benanderman/spork-8/Images/input-3d.png

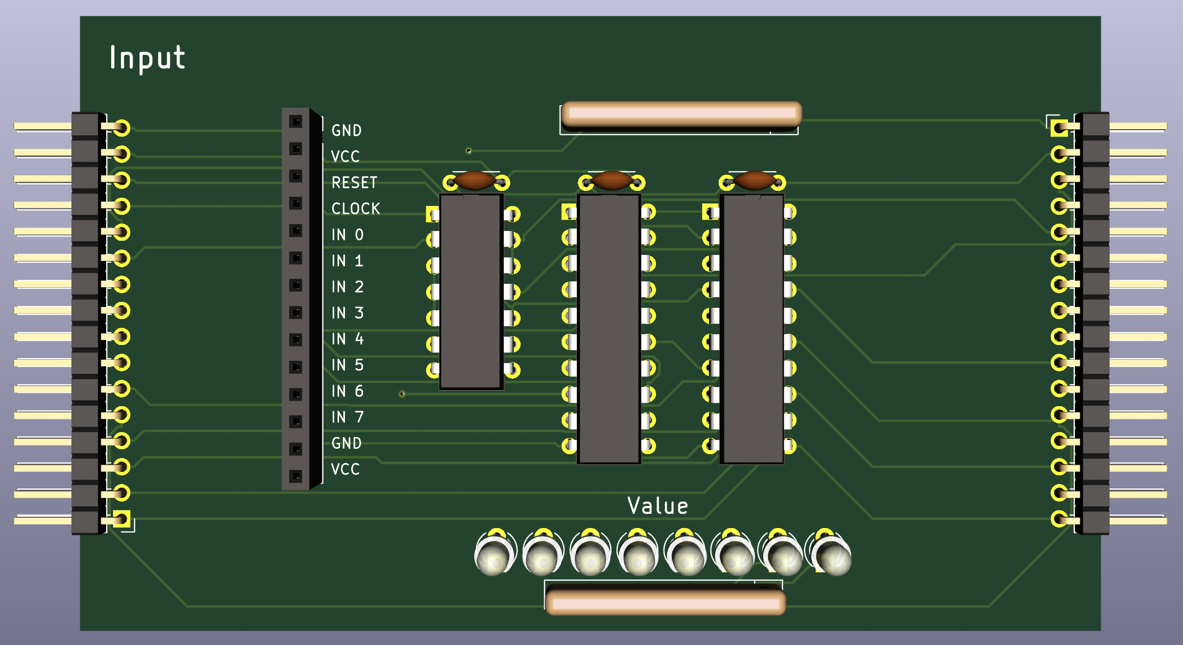
Images/input-3d.png
