benanderman/spork-8/Images/input-pcb.png

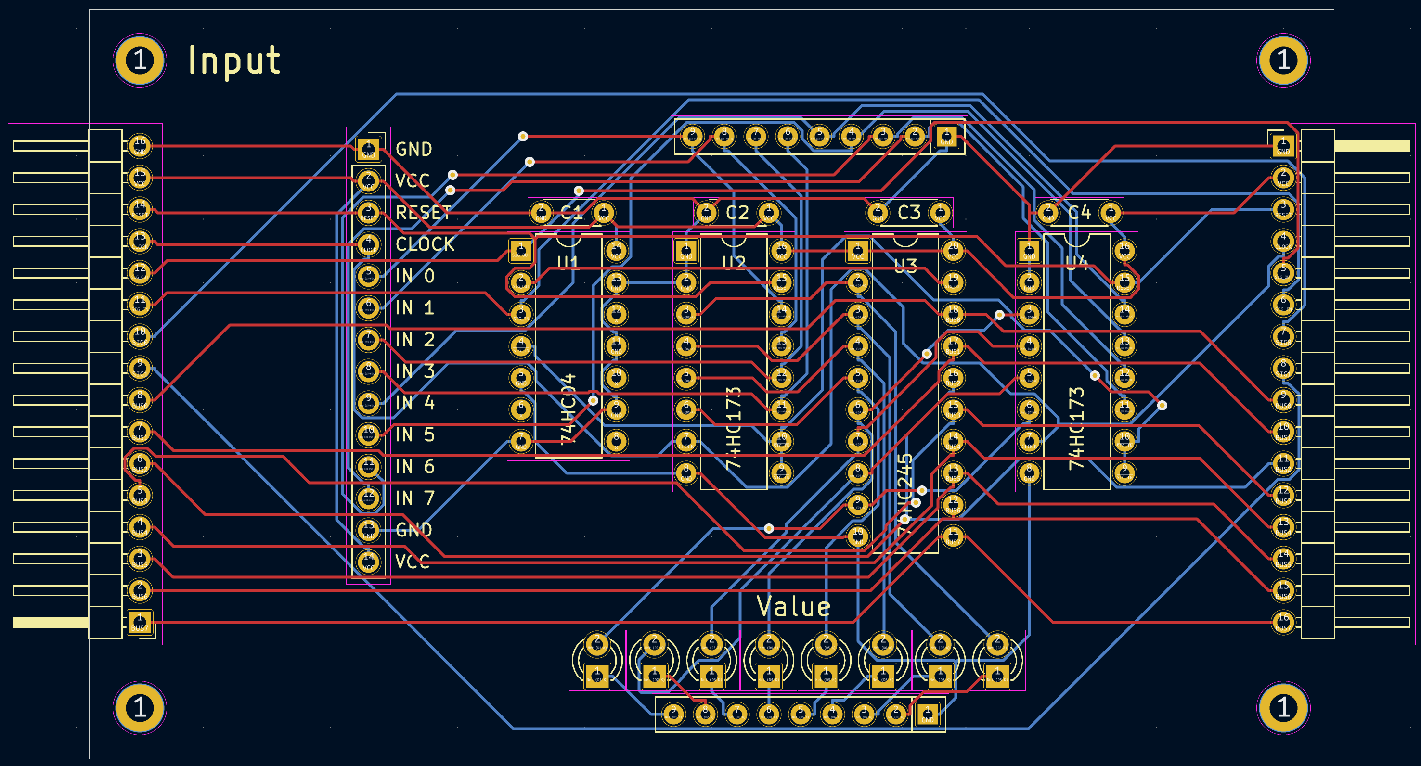
Images/input-pcb.png
