benanderman/spork-8/Images/input-sch.png

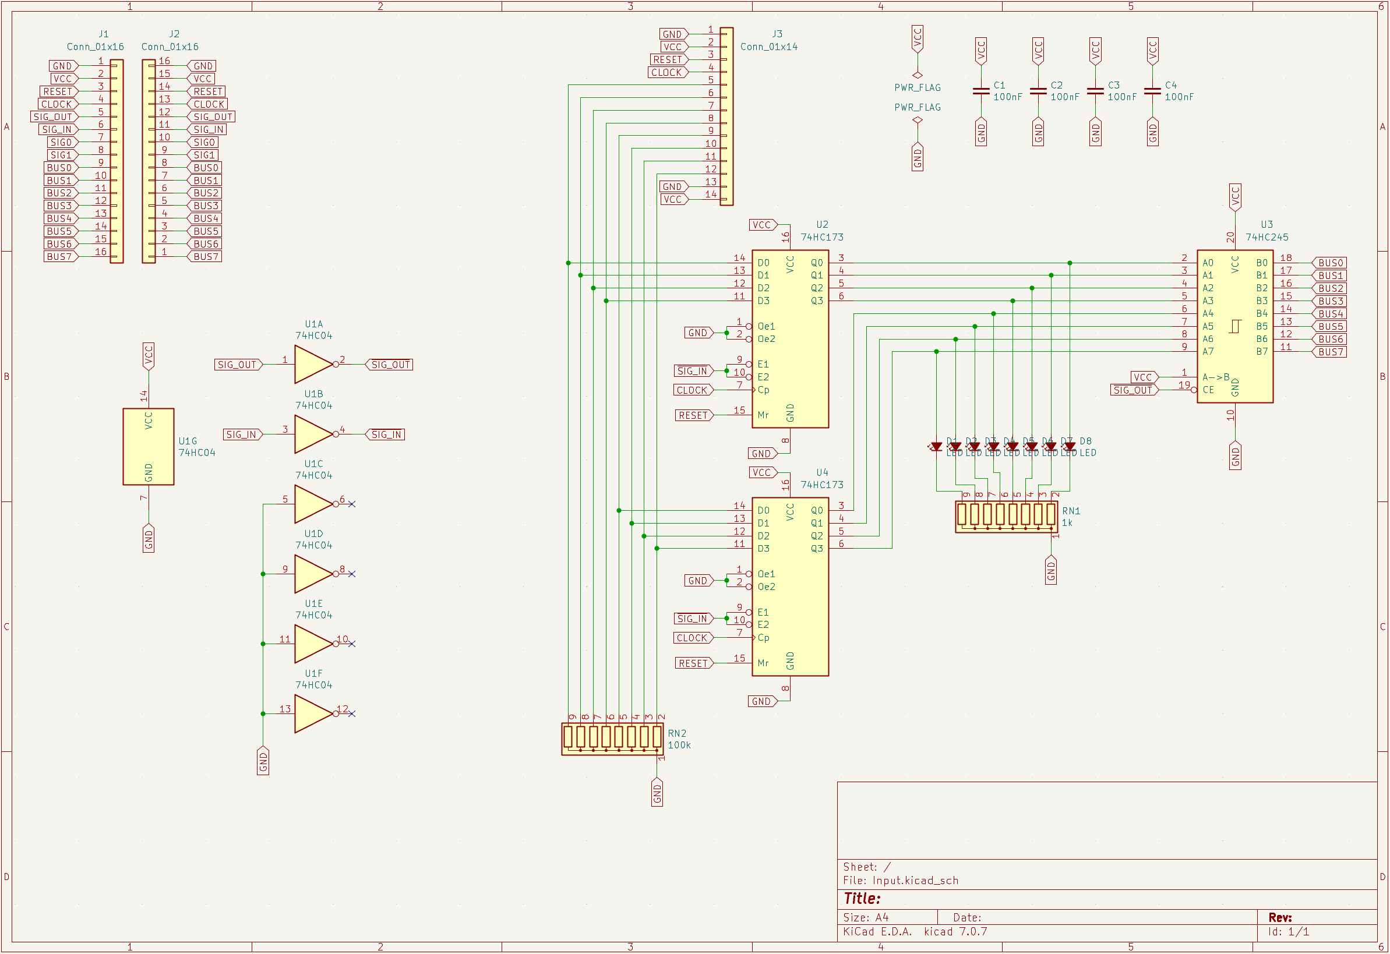
Images/input-sch.png
