benanderman/spork-8/ALU/ALU.kicad_pcb

## KiCad design ALU/ALU.kicad_pcb (2025-06-30)

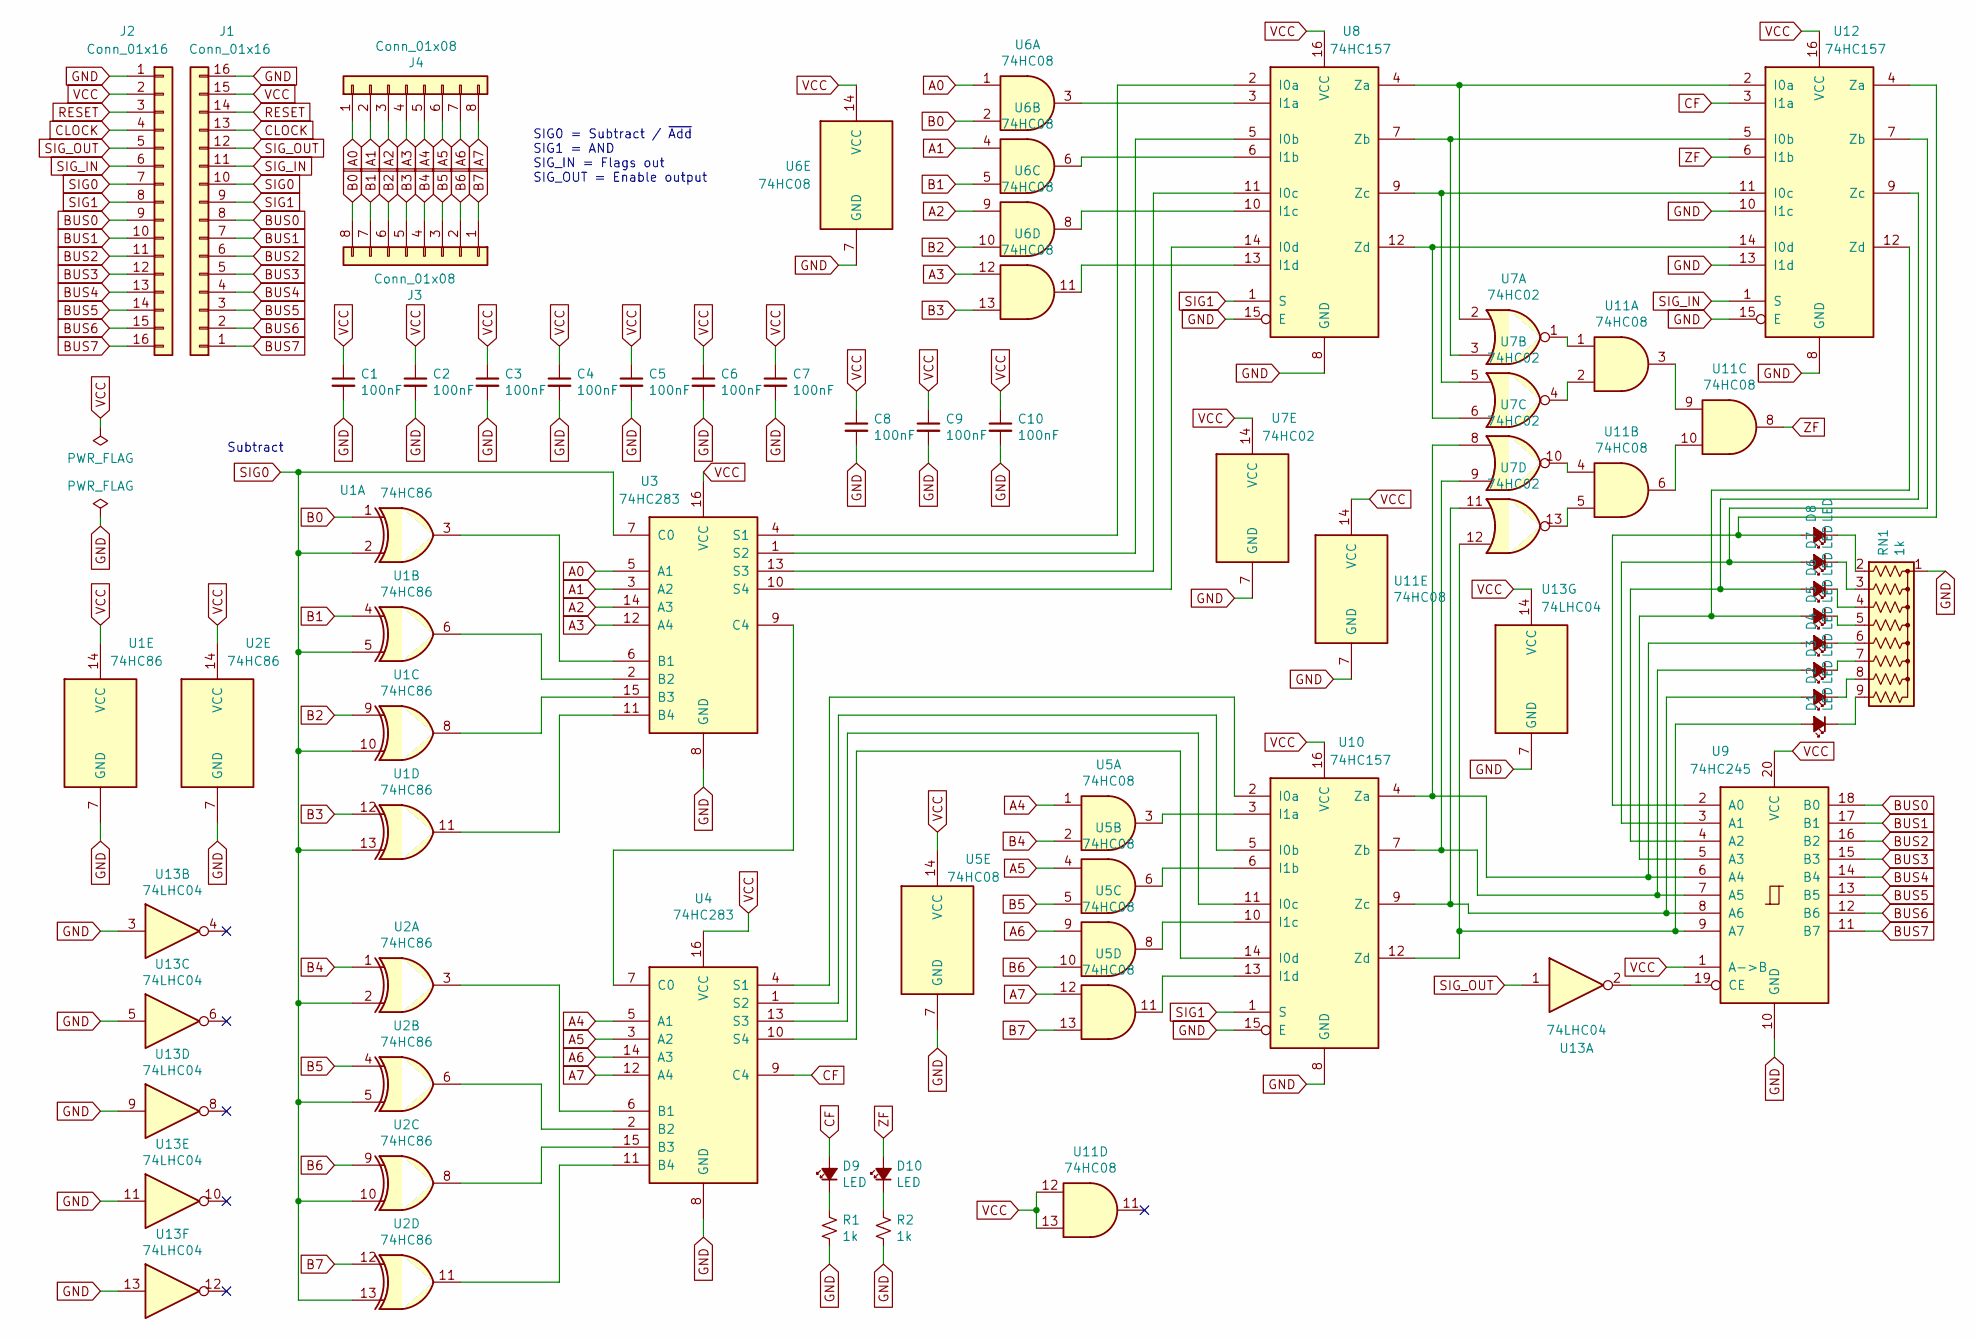
[picture p75: schematic ALU.kicad_sch]

Parts:
C1, C2, C3, C4, C5, C6, C7, C8, C9, C10: 100nF; C_Disc_D4.3mm_W1.9mm_P5.00mm
D1, D2, D3, D4, D5, D6, D7, D8, D9, D10: LED; LED_D3.0mm_Clear
J1, J2: Conn_01x16; PinHeader_1x16_P2.54mm_Horizontal
J3, J4: Conn_01x08; PinHeader_1x08_P2.54mm_Horizontal
R1, R2: 1k; R_Axial_DIN0207_L6.3mm_D2.5mm_P7.62mm_Horizontal
RN1: 1k; R_Array_SIP9
U1, U2: 74HC86; DIP-14_W7.62mm
U3, U4: 74HC283; DIP-16_W7.62mm
U5, U6, U11: 74HC08; DIP-14_W7.62mm
U7: 74HC02; DIP-14_W7.62mm
U8, U10, U12: 74HC157; DIP-16_W7.62mm
U9: 74HC245; DIP-20_W7.62mm
U13: 74LHC04; DIP-14_W7.62mm

Connections:
A0: J4.1, U3.5 (A1), U6.1
A1: J4.2, U3.3 (A2), U6.4
A2: J4.3, U3.14 (A3), U6.9
A3: J4.4, U3.12 (A4), U6.12
A4: J4.5, U4.5 (A1), U5.1
A5: J4.6, U4.3 (A2), U5.4
A6: J4.7, U4.14 (A3), U5.9
A7: J4.8, U4.12 (A4), U5.12
B0: J3.8, U1.1, U6.2
B1: J3.7, U1.4, U6.5
B2: J3.6, U1.9, U6.10
B3: J3.5, U1.12, U6.13
B4: J3.4, U2.1, U5.2
B5: J3.3, U2.4, U5.5
B6: J3.2, U2.9, U5.10
B7: J3.1, U2.12, U5.13
BUS0: J1.8, J2.9, U9.18 (B0)
BUS1: J1.7, J2.10, U9.17 (B1)
BUS2: J1.6, J2.11, U9.16 (B2)
BUS3: J1.5, J2.12, U9.15 (B3)
BUS4: J1.4, J2.13, U9.14 (B4)
BUS5: J1.3, J2.14, U9.13 (B5)
BUS6: J1.2, J2.15, U9.12 (B6)
BUS7: J1.1, J2.16, U9.11 (B7)
CF: D9.2 (A), U4.9 (C4), U12.3 (I1a)
CLOCK: J1.13, J2.4
GND: C1.2, C2.2, C3.2, C4.2, C5.2, C6.2, C7.2, C8.2, C9.2, C10.2, J1.16, J2.1, R1.2, R2.2, RN1.1 (common), U1.7 (GND), U2.7 (GND), U3.8 (GND), U4.8 (GND), U5.7 (GND), U6.7 (GND), U7.7 (GND), U8.8 (GND), U8.15 (E), U9.10 (GND), U10.8 (GND), U10.15 (E), U11.7 (GND), U12.8 (GND), U12.10 (I1c), U12.13 (I1d), U12.15 (E), U13.3, U13.5, U13.7 (GND), U13.9, U13.11, U13.13
unnamed: D1.2 (A), U7.12, U9.9 (A7), U10.12 (Zd)
unnamed: D1.1 (K), RN1.9 (R8)
unnamed: D2.2 (A), U7.11, U9.8 (A6), U10.9 (Zc)
unnamed: D2.1 (K), RN1.8 (R7)
unnamed: D3.2 (A), U7.9, U9.7 (A5), U10.7 (Zb)
unnamed: D3.1 (K), RN1.7 (R6)
unnamed: D4.2 (A), U7.8, U9.6 (A4), U10.4 (Za)
unnamed: D4.1 (K), RN1.6 (R5)
unnamed: D5.2 (A), U9.5 (A3), U12.12 (Zd)
unnamed: D5.1 (K), RN1.5 (R4)
unnamed: D6.2 (A), U9.4 (A2), U12.9 (Zc)
unnamed: D6.1 (K), RN1.4 (R3)
unnamed: D7.2 (A), U9.3 (A1), U12.7 (Zb)
unnamed: D7.1 (K), RN1.3 (R2)
unnamed: D8.2 (A), U9.2 (A0), U12.4 (Za)
unnamed: D8.1 (K), RN1.2 (R1)
unnamed: D9.1 (K), R1.1
unnamed: D10.1 (K), R2.1
unnamed: U1.3, U3.6 (B1)
unnamed: U1.6, U3.2 (B2)
unnamed: U1.8, U3.15 (B3)
unnamed: U1.11, U3.11 (B4)
unnamed: U3.9 (C4), U4.7 (C0)
unnamed: U3.4 (S1), U8.2 (I0a)
unnamed: U3.1 (S2), U8.5 (I0b)
unnamed: U3.13 (S3), U8.11 (I0c)
unnamed: U3.10 (S4), U8.14 (I0d)
unnamed: U2.3, U4.6 (B1)
unnamed: U2.6, U4.2 (B2)
unnamed: U2.8, U4.15 (B3)
unnamed: U2.11, U4.11 (B4)
unnamed: U6.3, U8.3 (I1a)
unnamed: U6.6, U8.6 (I1b)
unnamed: U6.8, U8.10 (I1c)
unnamed: U6.11, U8.13 (I1d)
unnamed: U9.19 (CE), U13.2
unnamed: U4.4 (S1), U10.2 (I0a)
unnamed: U4.1 (S2), U10.5 (I0b)
unnamed: U4.13 (S3), U10.11 (I0c)
unnamed: U4.10 (S4), U10.14 (I0d)
unnamed: U5.3, U10.3 (I1a)
unnamed: U5.6, U10.6 (I1b)
unnamed: U5.8, U10.10 (I1c)
unnamed: U5.11, U10.13 (I1d)
unnamed: U7.1, U11.1
unnamed: U7.4, U11.2
unnamed: U11.3, U11.9
unnamed: U7.10, U11.4
unnamed: U7.13, U11.5
unnamed: U11.6, U11.10
unnamed: U7.2, U8.4 (Za), U12.2 (I0a)
unnamed: U7.3, U8.7 (Zb), U12.5 (I0b)
unnamed: U7.5, U8.9 (Zc), U12.11 (I0c)
unnamed: U7.6, U8.12 (Zd), U12.14 (I0d)
RESET: J1.14, J2.3
SIG0: J1.10, J2.7, U1.2, U1.5, U1.10, U1.13, U2.2, U2.5, U2.10, U2.13, U3.7 (C0)
SIG1: J1.9, J2.8, U8.1 (S), U10.1 (S)
SIG_IN: J1.11, J2.6, U12.1 (S)
SIG_OUT: J1.12, J2.5, U13.1
VCC: C1.1, C2.1, C3.1, C4.1, C5.1, C6.1, C7.1, C8.1, C9.1, C10.1, J1.15, J2.2, U1.14 (VCC), U2.14 (VCC), U3.16 (VCC), U4.16 (VCC), U5.14 (VCC), U6.14 (VCC), U7.14 (VCC), U8.16 (VCC), U9.1 (A->B), U9.20 (VCC), U10.16 (VCC), U11.12, U11.13, U11.14 (VCC), U12.16 (VCC), U13.14 (VCC)
ZF: D10.2 (A), U11.8, U12.6 (I1b)

Notes on the sheet:
Subtract
SIG0 = Subtract / ~{Add} SIG1 = AND SIG_IN = Flags out SIG_OUT = Enable output

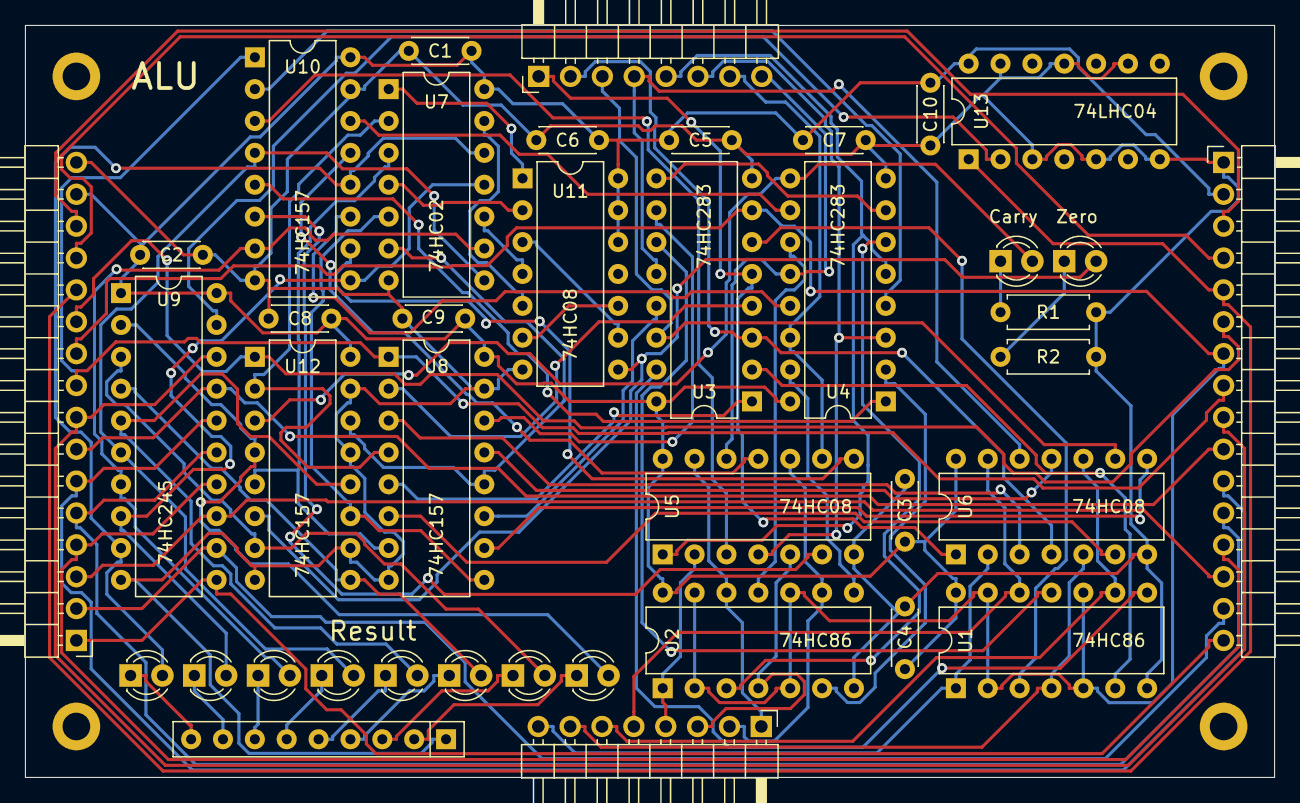
[picture p76: board ALU.kicad_pcb from above]

Board: 2 copper layers, 99.6 x 59.9 mm, 44 parts (0 on the bottom side), 88 nets.

Other parts of the board:
HOLE1, HOLE2, HOLE3, HOLE4: MountingHole_2.2mm_M2_DIN965_Pad
