benanderman/spork-8/Counter/Counter.kicad_pcb

## KiCad design Counter/Counter.kicad_pcb (2025-06-30)

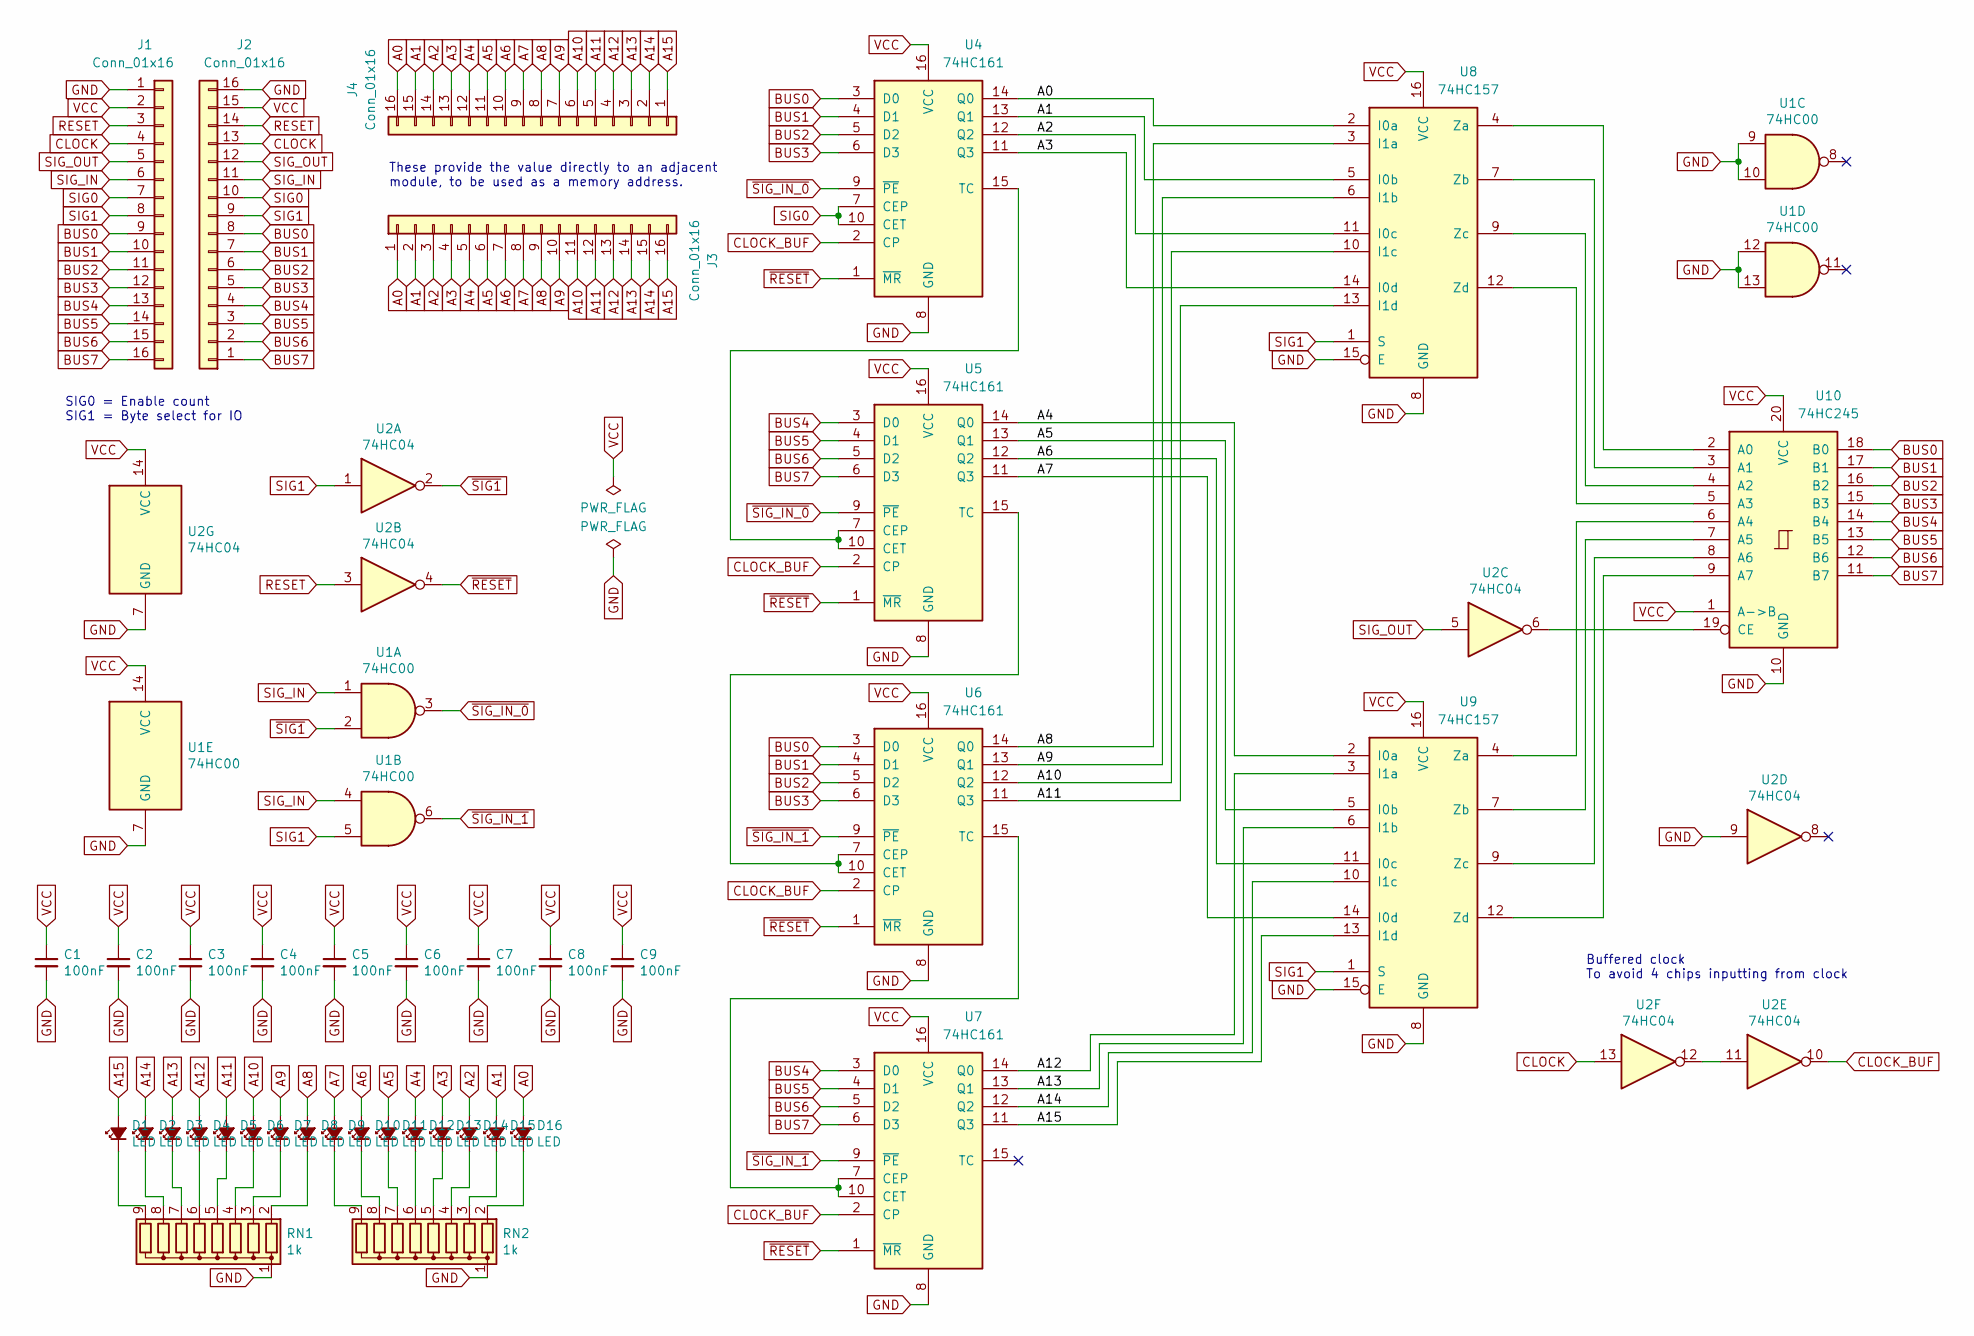
[picture p77: schematic Counter.kicad_sch]

Parts:
C1, C2, C3, C4, C5, C6, C7, C8, C9: 100nF; C_Disc_D4.3mm_W1.9mm_P5.00mm
D1, D2, D3, D4, D5, D6, D7, D8, D9, D10, D11, D12, D13, D14, D15, D16: LED; LED_D3.0mm
J1, J2: Conn_01x16; PinHeader_1x16_P2.54mm_Horizontal
J3, J4: Conn_01x16; PinSocket_1x16_P2.54mm_Horizontal
RN1, RN2: 1k; R_Array_SIP9
U1: 74HC00; DIP-14_W7.62mm
U2: 74HC04; DIP-14_W7.62mm
U4, U5, U6, U7: 74HC161; DIP-16_W7.62mm
U8, U9: 74HC157; DIP-16_W7.62mm
U10: 74HC245; DIP-20_W7.62mm

Connections:
A0: D16.2 (A), J3.1, J4.16, U4.14 (Q0), U8.2 (I0a)
A1: D15.2 (A), J3.2, J4.15, U4.13 (Q1), U8.5 (I0b)
A2: D14.2 (A), J3.3, J4.14, U4.12 (Q2), U8.11 (I0c)
A3: D13.2 (A), J3.4, J4.13, U4.11 (Q3), U8.14 (I0d)
A4: D12.2 (A), J3.5, J4.12, U5.14 (Q0), U9.2 (I0a)
A5: D11.2 (A), J3.6, J4.11, U5.13 (Q1), U9.5 (I0b)
A6: D10.2 (A), J3.7, J4.10, U5.12 (Q2), U9.11 (I0c)
A7: D9.2 (A), J3.8, J4.9, U5.11 (Q3), U9.14 (I0d)
A8: D8.2 (A), J3.9, J4.8, U6.14 (Q0), U8.3 (I1a)
A9: D7.2 (A), J3.10, J4.7, U6.13 (Q1), U8.6 (I1b)
A10: D6.2 (A), J3.11, J4.6, U6.12 (Q2), U8.10 (I1c)
A11: D5.2 (A), J3.12, J4.5, U6.11 (Q3), U8.13 (I1d)
A12: D4.2 (A), J3.13, J4.4, U7.14 (Q0), U9.3 (I1a)
A13: D3.2 (A), J3.14, J4.3, U7.13 (Q1), U9.6 (I1b)
A14: D2.2 (A), J3.15, J4.2, U7.12 (Q2), U9.10 (I1c)
A15: D1.2 (A), J3.16, J4.1, U7.11 (Q3), U9.13 (I1d)
BUS0: J1.9, J2.8, U4.3 (D0), U6.3 (D0), U10.18 (B0)
BUS1: J1.10, J2.7, U4.4 (D1), U6.4 (D1), U10.17 (B1)
BUS2: J1.11, J2.6, U4.5 (D2), U6.5 (D2), U10.16 (B2)
BUS3: J1.12, J2.5, U4.6 (D3), U6.6 (D3), U10.15 (B3)
BUS4: J1.13, J2.4, U5.3 (D0), U7.3 (D0), U10.14 (B4)
BUS5: J1.14, J2.3, U5.4 (D1), U7.4 (D1), U10.13 (B5)
BUS6: J1.15, J2.2, U5.5 (D2), U7.5 (D2), U10.12 (B6)
BUS7: J1.16, J2.1, U5.6 (D3), U7.6 (D3), U10.11 (B7)
CLOCK: J1.4, J2.13, U2.13
CLOCK_BUF: U2.10, U4.2 (CP), U5.2 (CP), U6.2 (CP), U7.2 (CP)
GND: C1.2, C2.2, C3.2, C4.2, C5.2, C6.2, C7.2, C8.2, C9.2, J1.1, J2.16, RN1.1 (common), RN2.1 (common), U1.7 (GND), U1.9, U1.10, U1.12, U1.13, U2.7 (GND), U2.9, U4.8 (GND), U5.8 (GND), U6.8 (GND), U7.8 (GND), U8.8 (GND), U8.15 (E), U9.8 (GND), U9.15 (E), U10.10 (GND)
unnamed: D1.1 (K), RN1.9 (R8)
unnamed: D2.1 (K), RN1.8 (R7)
unnamed: D3.1 (K), RN1.7 (R6)
unnamed: D4.1 (K), RN1.6 (R5)
unnamed: D5.1 (K), RN1.5 (R4)
unnamed: D6.1 (K), RN1.4 (R3)
unnamed: D7.1 (K), RN1.3 (R2)
unnamed: D8.1 (K), RN1.2 (R1)
unnamed: D9.1 (K), RN2.9 (R8)
unnamed: D10.1 (K), RN2.8 (R7)
unnamed: D11.1 (K), RN2.7 (R6)
unnamed: D12.1 (K), RN2.6 (R5)
unnamed: D13.1 (K), RN2.5 (R4)
unnamed: D14.1 (K), RN2.4 (R3)
unnamed: D15.1 (K), RN2.3 (R2)
unnamed: D16.1 (K), RN2.2 (R1)
unnamed: U2.11, U2.12
unnamed: U4.15 (TC), U5.7 (CEP), U5.10 (CET)
unnamed: U5.15 (TC), U6.7 (CEP), U6.10 (CET)
unnamed: U6.15 (TC), U7.7 (CEP), U7.10 (CET)
unnamed: U8.4 (Za), U10.2 (A0)
unnamed: U8.7 (Zb), U10.3 (A1)
unnamed: U8.9 (Zc), U10.4 (A2)
unnamed: U8.12 (Zd), U10.5 (A3)
unnamed: U9.4 (Za), U10.6 (A4)
unnamed: U9.7 (Zb), U10.7 (A5)
unnamed: U9.9 (Zc), U10.8 (A6)
unnamed: U9.12 (Zd), U10.9 (A7)
unnamed: U2.6, U10.19 (CE)
RESET: J1.3, J2.14, U2.3
SIG0: J1.7, J2.10, U4.7 (CEP), U4.10 (CET)
SIG1: J1.8, J2.9, U1.5, U2.1, U8.1 (S), U9.1 (S)
SIG_IN: J1.6, J2.11, U1.1, U1.4
SIG_OUT: J1.5, J2.12, U2.5
VCC: C1.1, C2.1, C3.1, C4.1, C5.1, C6.1, C7.1, C8.1, C9.1, J1.2, J2.15, U1.14 (VCC), U2.14 (VCC), U4.16 (VCC), U5.16 (VCC), U6.16 (VCC), U7.16 (VCC), U8.16 (VCC), U9.16 (VCC), U10.1 (A->B), U10.20 (VCC)
~RESET: U2.4, U4.1 (~MR), U5.1 (~MR), U6.1 (~MR), U7.1 (~MR)
~SIG1: U1.2, U2.2
~SIG_IN_0: U1.3, U4.9 (~PE), U5.9 (~PE)
~SIG_IN_1: U1.6, U6.9 (~PE), U7.9 (~PE)

Notes on the sheet:
Buffered clock To avoid 4 chips inputting from clock
SIG0 = Enable count SIG1 = Byte select for IO
These provide the value directly to an adjacent module, to be used as a memory address.

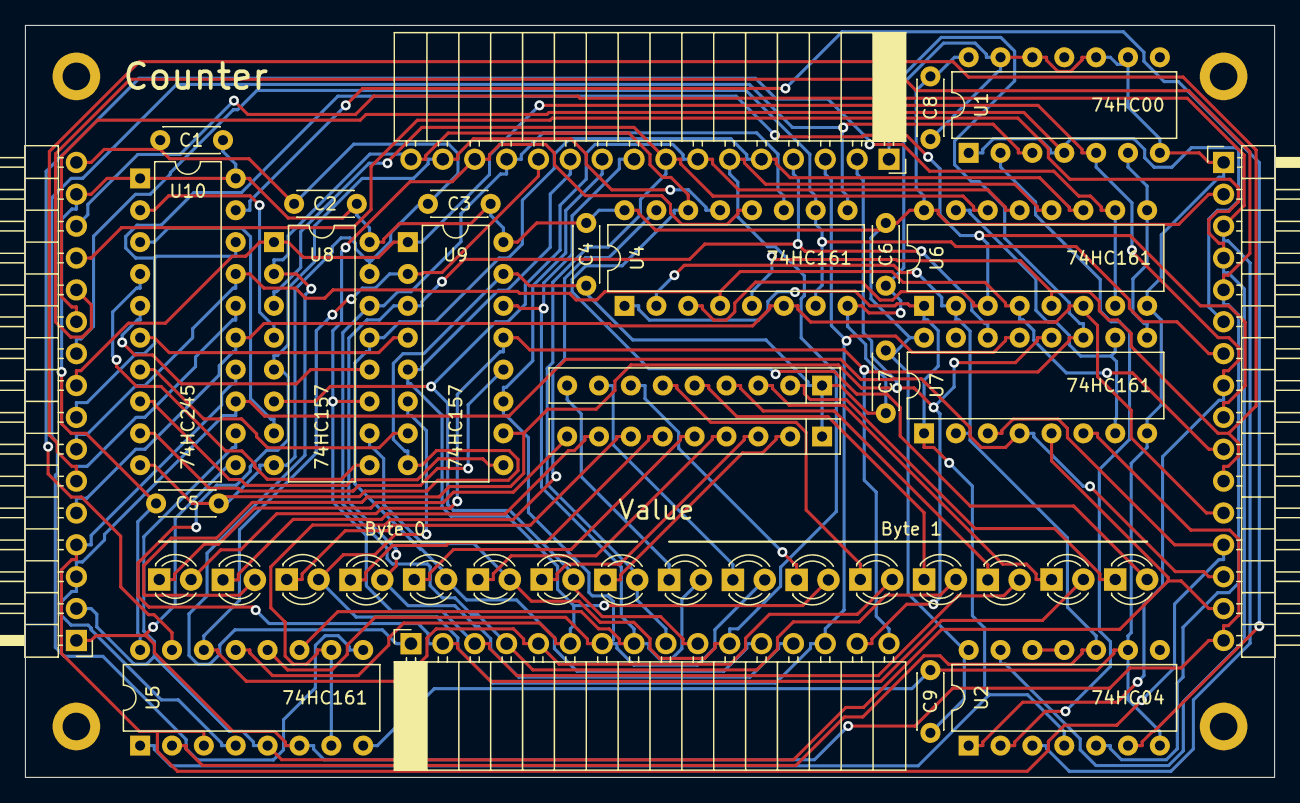
[picture p78: board Counter.kicad_pcb from above]

Board: 2 copper layers, 99.6 x 59.9 mm, 44 parts (0 on the bottom side), 66 nets.

Other parts of the board:
HOLE1, HOLE2, HOLE3, HOLE4: MountingHole_2.2mm_M2_DIN965_Pad
