benanderman/spork-8/Code/programs.cpp

#include "programs.h"

uint8_t getJumpToCartridgeByte(unsigned int address) {
  static const unsigned char PROGMEM data[] = {
    /* 0x00 */ 0x68, 0x80, 0x00
  };
  int len = sizeof(data) / sizeof(*data);
  return address < len ? pgm_read_byte(&data[address]) : 0;
}

uint8_t getMovingDotByte(unsigned int address) {
  static const unsigned char PROGMEM data[] = {
0x11, 0x04, 0x30, 0x00, 0x00, 0x11, 0x01, 0x30, 0x00, 0x01, 0x66, 0x80, 0x8e, 0x11, 0x01, 0x16, 
0x00, 0x16, 0x02, 0x16, 0x00, 0x16, 0x01, 0x87, 0x69, 0x80, 0x7e, 0x16, 0x03, 0x16, 0x01, 0x87, 
0x69, 0x80, 0x5e, 0x16, 0x03, 0x16, 0x01, 0x87, 0x69, 0x80, 0x6e, 0x16, 0x03, 0x16, 0x01, 0x87, 
0x69, 0x80, 0x4e, 0x16, 0x03, 0x16, 0x01, 0x87, 0x69, 0x80, 0xd6, 0x16, 0x03, 0x16, 0x01, 0x87, 
0x69, 0x80, 0xf5, 0x16, 0x03, 0x16, 0x01, 0x16, 0x03, 0x16, 0x01, 0x66, 0x80, 0x0d, 0x0a, 0x00, 
0x01, 0x79, 0x00, 0x67, 0x80, 0x8e, 0x9e, 0x01, 0x30, 0x00, 0x01, 0x66, 0x80, 0x8e, 0x0a, 0x00, 
0x01, 0x99, 0x01, 0x79, 0x14, 0x67, 0x80, 0x8e, 0x30, 0x00, 0x01, 0x66, 0x80, 0x8e, 0x0a, 0x00, 
0x00, 0x79, 0x00, 0x67, 0x80, 0x8e, 0x9e, 0x01, 0x30, 0x00, 0x00, 0x66, 0x80, 0x8e, 0x0a, 0x00, 
0x00, 0x99, 0x01, 0x79, 0x0a, 0x67, 0x80, 0x8e, 0x30, 0x00, 0x00, 0x66, 0x80, 0x8e, 0x11, 0x00, 
0x30, 0x00, 0x02, 0x11, 0x00, 0x30, 0x00, 0x03, 0x0a, 0x00, 0x00, 0x7b, 0x00, 0x03, 0x69, 0x80, 
0xb1, 0x0a, 0x00, 0x01, 0x7b, 0x00, 0x02, 0x69, 0x80, 0xb1, 0x15, 0x01, 0x15, 0x03, 0x66, 0x80, 
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
0x82, 0x69, 0x15, 0x01, 0x15, 0x03, 0x68, 0x82, 0x6d, 0x15, 0x00, 0x15, 0x02, 0x0a, 0x00, 0x17, 
0x9c, 0x01, 0x2e, 0x00, 0x17, 0x6a, 0x82, 0x59, 0x15, 0x04, 0x15, 0x00, 0x68, 0x80, 0x61
  };
  int len = sizeof(data) / sizeof(*data);
  return address < len ? pgm_read_byte(&data[address]) : 0;
}
