benanderman/spork-8/Code/instruction_set.cpp

#include "instruction_set.h"
#include "instructions.h"
#include "signals.h"

uint8_t getMicrocodeHighByte(uint16_t address) {
  return getMicrocode(address) >> 8;
}

uint8_t getMicrocodeLowByte(uint16_t address) {
  return getMicrocode(address) & 0xFF;
}

#define INSTRUCTION if (index-- == 0) return Instruction

Instruction getInstruction(uint8_t index) {
  // const Instruction instructions[] = {
  INSTRUCTION(Instruction::Type::SetPageReg, Instruction::FlagsMask::UNCONDITIONAL, 0, REGA);
  INSTRUCTION(Instruction::Type::SetPageReg, Instruction::FlagsMask::UNCONDITIONAL, 0, REGB);
  INSTRUCTION(Instruction::Type::SetPageReg, Instruction::FlagsMask::UNCONDITIONAL, 0, REGC);
  INSTRUCTION(Instruction::Type::SetPageReg, Instruction::FlagsMask::UNCONDITIONAL, 0, SWAP);
  INSTRUCTION(Instruction::Type::SetPageI,   Instruction::FlagsMask::UNCONDITIONAL, 1);

  INSTRUCTION(Instruction::Type::SetAddrReg, Instruction::FlagsMask::UNCONDITIONAL, 0, REGA);
  INSTRUCTION(Instruction::Type::SetAddrReg, Instruction::FlagsMask::UNCONDITIONAL, 0, REGB);
  INSTRUCTION(Instruction::Type::SetAddrReg, Instruction::FlagsMask::UNCONDITIONAL, 0, REGC);
  INSTRUCTION(Instruction::Type::SetAddrReg, Instruction::FlagsMask::UNCONDITIONAL, 0, SWAP);
  INSTRUCTION(Instruction::Type::SetAddrI,   Instruction::FlagsMask::UNCONDITIONAL, 1);

  INSTRUCTION(Instruction::Type::Load,      Instruction::FlagsMask::UNCONDITIONAL, 2, REGA);
  INSTRUCTION(Instruction::Type::Load,      Instruction::FlagsMask::UNCONDITIONAL, 2, REGB);
  INSTRUCTION(Instruction::Type::Load,      Instruction::FlagsMask::UNCONDITIONAL, 2, REGC);
  INSTRUCTION(Instruction::Type::Load,      Instruction::FlagsMask::UNCONDITIONAL, 2, SWAP);
  INSTRUCTION(Instruction::Type::Load,      Instruction::FlagsMask::UNCONDITIONAL, 2, OUTA);
  INSTRUCTION(Instruction::Type::Load,      Instruction::FlagsMask::UNCONDITIONAL, 2, IOA);
  INSTRUCTION(Instruction::Type::Load,      Instruction::FlagsMask::UNCONDITIONAL, 2, IOB);

  INSTRUCTION(Instruction::Type::LoadI,     Instruction::FlagsMask::UNCONDITIONAL, 1, REGA);
  INSTRUCTION(Instruction::Type::LoadI,     Instruction::FlagsMask::UNCONDITIONAL, 1, REGB);
  INSTRUCTION(Instruction::Type::LoadI,     Instruction::FlagsMask::UNCONDITIONAL, 1, REGC);
  INSTRUCTION(Instruction::Type::LoadI,     Instruction::FlagsMask::UNCONDITIONAL, 1, SWAP);
  INSTRUCTION(Instruction::Type::LoadI,     Instruction::FlagsMask::UNCONDITIONAL, 1, OUTA);
  INSTRUCTION(Instruction::Type::LoadI,     Instruction::FlagsMask::UNCONDITIONAL, 1, IOA);
  INSTRUCTION(Instruction::Type::LoadI,     Instruction::FlagsMask::UNCONDITIONAL, 1, IOB);

  INSTRUCTION(Instruction::Type::LoadP,     Instruction::FlagsMask::UNCONDITIONAL, 1, REGA);
  INSTRUCTION(Instruction::Type::LoadP,     Instruction::FlagsMask::UNCONDITIONAL, 1, REGB);
  INSTRUCTION(Instruction::Type::LoadP,     Instruction::FlagsMask::UNCONDITIONAL, 1, REGC);
  INSTRUCTION(Instruction::Type::LoadP,     Instruction::FlagsMask::UNCONDITIONAL, 1, SWAP);
  INSTRUCTION(Instruction::Type::LoadP,     Instruction::FlagsMask::UNCONDITIONAL, 1, OUTA);
  INSTRUCTION(Instruction::Type::LoadP,     Instruction::FlagsMask::UNCONDITIONAL, 1, IOA);
  INSTRUCTION(Instruction::Type::LoadP,     Instruction::FlagsMask::UNCONDITIONAL, 1, IOB);

  INSTRUCTION(Instruction::Type::LoadInc,   Instruction::FlagsMask::UNCONDITIONAL, 0, REGA, 0);
  INSTRUCTION(Instruction::Type::LoadInc,   Instruction::FlagsMask::UNCONDITIONAL, 0, REGB, 0);
  INSTRUCTION(Instruction::Type::LoadInc,   Instruction::FlagsMask::UNCONDITIONAL, 0, REGC, 0);
  INSTRUCTION(Instruction::Type::LoadInc,   Instruction::FlagsMask::UNCONDITIONAL, 0, SWAP, 0);
  INSTRUCTION(Instruction::Type::LoadInc,   Instruction::FlagsMask::UNCONDITIONAL, 0, OUTA, 0);

  INSTRUCTION(Instruction::Type::LoadInc,   Instruction::FlagsMask::UNCONDITIONAL, 0, REGA, 1);
  INSTRUCTION(Instruction::Type::LoadInc,   Instruction::FlagsMask::UNCONDITIONAL, 0, REGB, 1);
  INSTRUCTION(Instruction::Type::LoadInc,   Instruction::FlagsMask::UNCONDITIONAL, 0, REGC, 1);
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
  INSTRUCTION(Instruction::Type::And,       Instruction::FlagsMask::CF | Instruction::FlagsMask::NO_FLAGS, 2);
  INSTRUCTION(Instruction::Type::And,       Instruction::FlagsMask::ZF | Instruction::FlagsMask::NO_FLAGS, 2);

  INSTRUCTION(Instruction::Type::Or,        Instruction::FlagsMask::UNCONDITIONAL, 2);
  INSTRUCTION(Instruction::Type::Or,        Instruction::FlagsMask::ZF | Instruction::FlagsMask::ZF_CF, 2);
  INSTRUCTION(Instruction::Type::Or,        Instruction::FlagsMask::CF | Instruction::FlagsMask::ZF_CF, 2);
  INSTRUCTION(Instruction::Type::Or,        Instruction::FlagsMask::CF | Instruction::FlagsMask::NO_FLAGS, 2);
  INSTRUCTION(Instruction::Type::Or,        Instruction::FlagsMask::ZF | Instruction::FlagsMask::NO_FLAGS, 2);

  INSTRUCTION(Instruction::Type::Xor,       Instruction::FlagsMask::UNCONDITIONAL, 2);
  INSTRUCTION(Instruction::Type::Xor,       Instruction::FlagsMask::ZF | Instruction::FlagsMask::ZF_CF, 2);
  INSTRUCTION(Instruction::Type::Xor,       Instruction::FlagsMask::CF | Instruction::FlagsMask::ZF_CF, 2);
  INSTRUCTION(Instruction::Type::Xor,       Instruction::FlagsMask::CF | Instruction::FlagsMask::NO_FLAGS, 2);
  INSTRUCTION(Instruction::Type::Xor,       Instruction::FlagsMask::ZF | Instruction::FlagsMask::NO_FLAGS, 2);

  INSTRUCTION(Instruction::Type::Nop,       Instruction::FlagsMask::UNCONDITIONAL, 0);
  INSTRUCTION(Instruction::Type::Nop1,      Instruction::FlagsMask::UNCONDITIONAL, 0);
  INSTRUCTION(Instruction::Type::Nop2,      Instruction::FlagsMask::UNCONDITIONAL, 0);

  INSTRUCTION(Instruction::Type::Halt,      Instruction::FlagsMask::UNCONDITIONAL, 0);
  // };

  return Instruction(Instruction::Type::Nop, Instruction::FlagsMask::UNCONDITIONAL, 0);
  // const Instruction noop = Instruction(Instruction::Type::Nop, Instruction::FlagsMask::UNCONDITIONAL, 0);
  // return index < sizeof(instructions) / sizeof(*instructions) ? instructions[index] : noop;
}

uint16_t getMicrocode(uint16_t address) {
  uint8_t mi = address & 0b001111;
  uint8_t flags = 1 << ((address & 0b110000) >> 4);
  uint8_t inst = address >> 6;

  const Instruction instruction = getInstruction(inst);
  return instruction.microCodeForCycleFlags(mi, flags);
}
